potpurri/USB-C_PD_Board_V2_CYPD3177/imgs/v2.0/pcb-front.png

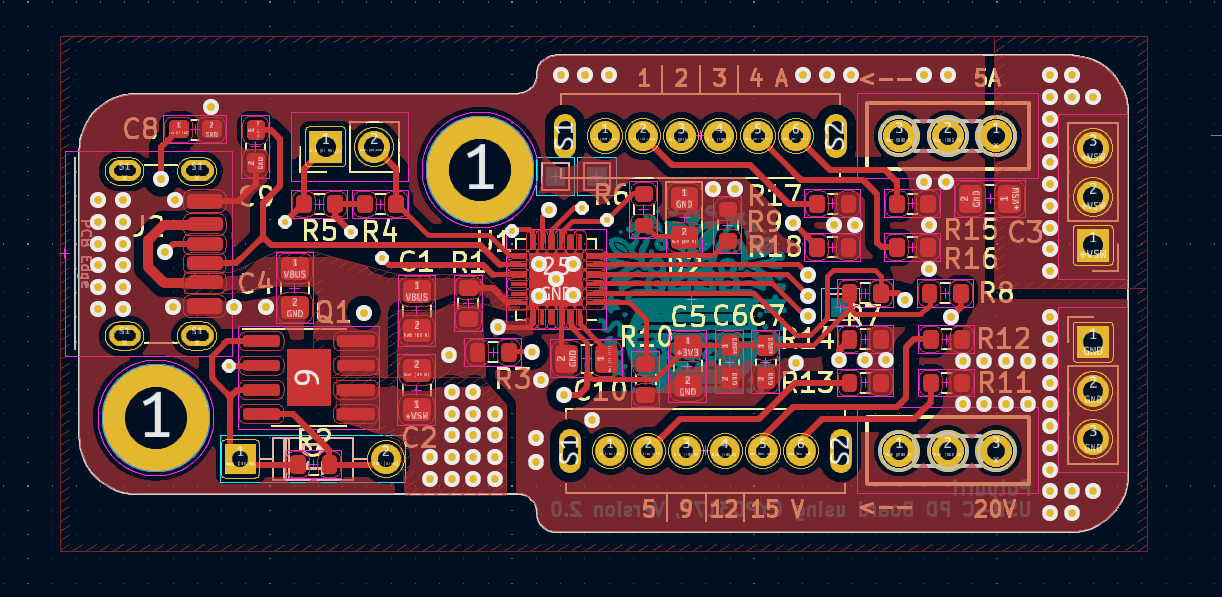
imgs/v2.0/pcb-front.png
